danjulio/firecam/firecam_app/pictures/firecam_utility_wifi_mac.png

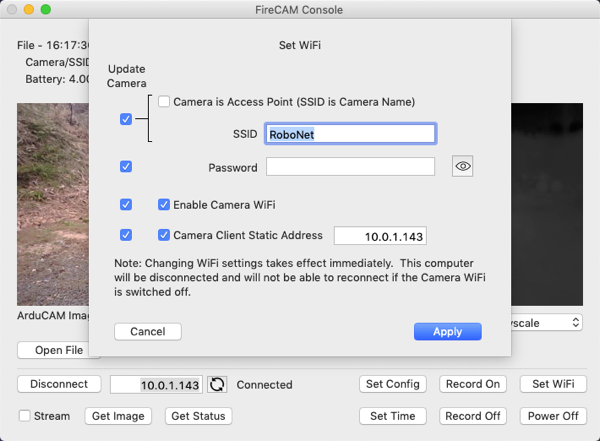
firecam_app/pictures/firecam_utility_wifi_mac.png
