danjulio/firecam/firmware/components/i2c/i2c.c

/*
 * I2C Module
 *
 * Provides I2C Access routines for other modules/tasks.  Provides a locking mechanism
 * since the underlying ESP IDF routines are not thread safe.
 *
 * Copyright 2020 Dan Julio
 *
 * This file is part of firecam.
 *
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
 */
#include "system_config.h"
#include "i2c.h"
#include "driver/i2c.h"
#include "freertos/FreeRTOS.h"
#include "freertos/semphr.h"


//
// I2C variables
//
static SemaphoreHandle_t i2c_mutex;



//
// I2C API
//

/**
 * i2c master initialization
 */
esp_err_t i2c_master_init()
{
    int i2c_master_port = I2C_MASTER_NUM;
    i2c_config_t conf;
    
    i2c_mutex = xSemaphoreCreateMutex();
    
    conf.mode = I2C_MODE_MASTER;
    conf.sda_io_num = I2C_MASTER_SDA_IO;
    conf.sda_pullup_en = GPIO_PULLUP_ENABLE;
    conf.scl_io_num = I2C_MASTER_SCL_IO;
    conf.scl_pullup_en = GPIO_PULLUP_ENABLE;
    conf.master.clk_speed = I2C_MASTER_FREQ_HZ;
    
    i2c_param_config(i2c_master_port, &conf);
    
    return i2c_driver_install(i2c_master_port, conf.mode,
                              I2C_MASTER_RX_BUF_LEN,
                              I2C_MASTER_TX_BUF_LEN, 0);
}


/**
 * i2c master lock
 */
void i2c_lock()
{
	xSemaphoreTake(i2c_mutex, portMAX_DELAY);
}


/**
 * i2c master unlock
 */
void i2c_unlock()
{
	xSemaphoreGive(i2c_mutex);
}


/**
 * Read esp-i2c-slave
 *
 * _______________________________________________________________________________________
 * | start | slave_addr + rd_bit +ack | read n-1 bytes + ack | read 1 byte + nack | stop |
 * --------|--------------------------|----------------------|--------------------|------|
 *
 */
esp_err_t i2c_master_read_slave(uint8_t addr7, uint8_t *data_rd, size_t size)
{
    if (size == 0) {
        return ESP_OK;
    }
    i2c_cmd_handle_t cmd = i2c_cmd_link_create();
    i2c_master_start(cmd);
    i2c_master_write_byte(cmd, (addr7 << 1) | I2C_MASTER_READ, ACK_CHECK_EN);
    if (size > 1) {
        i2c_master_read(cmd, data_rd, size - 1, ACK_VAL);
    }
    i2c_master_read_byte(cmd, data_rd + size - 1, NACK_VAL);
    i2c_master_stop(cmd);
    esp_err_t ret = i2c_master_cmd_begin(I2C_MODE_MASTER, cmd, 1000 / portTICK_RATE_MS);
    i2c_cmd_link_delete(cmd);
    return ret;
}


/**
 * Write esp-i2c-slave
 *
 * ___________________________________________________________________
 * | start | slave_addr + wr_bit + ack | write n bytes + ack  | stop |
 * --------|---------------------------|----------------------|------|
 *
 */
esp_err_t i2c_master_write_slave(uint8_t addr7, uint8_t *data_wr, size_t size)
{
    i2c_cmd_handle_t cmd = i2c_cmd_link_create();
    i2c_master_start(cmd);
    i2c_master_write_byte(cmd, (addr7 << 1) | I2C_MASTER_WRITE, ACK_CHECK_EN);
    i2c_master_write(cmd, data_wr, size, ACK_CHECK_EN);
    i2c_master_stop(cmd);
    esp_err_t ret = i2c_master_cmd_begin(I2C_MODE_MASTER, cmd, 1000 / portTICK_RATE_MS);
    i2c_cmd_link_delete(cmd);
    return ret;
}
