danjulio/firecam/firmware/components/lvgl_ili9341/ili9341.c

/**
 * @file ili9341.c
 *
 * Official lvgl esp32 port, ported to firecam by Dan Julio
 */

/*********************
 *      INCLUDES
 *********************/
#include "ili9341.h"
#include "disp_spi.h"
#include "driver/gpio.h"
#include "esp_log.h"
#include "freertos/FreeRTOS.h"
#include "freertos/task.h"
#include "sys_utilities.h"

/*********************
 *      DEFINES
 *********************/

/**********************
 *      TYPEDEFS
 **********************/

/*The LCD needs a bunch of command/argument values to be initialized. They are stored in this struct. */
typedef struct {
    uint8_t cmd;
    uint8_t data[16];
    uint8_t databytes; //No of data in data; bit 7 = delay after set; 0xFF = end of cmds.
} lcd_init_cmd_t;

/**********************
 *  STATIC PROTOTYPES
 **********************/
static void ili9341_send_cmd(uint8_t cmd);
static void ili9341_send_data(void * data, uint16_t length);
static void ili9341_send_color(void * data, uint16_t length);

/**********************
 *  STATIC VARIABLES
 **********************/
static const char* TAG = "ili9341";

/**********************
 *      MACROS
 **********************/

/**********************
 *   GLOBAL FUNCTIONS
 **********************/

void ili9341_init(void)
{
	lcd_init_cmd_t ili_init_cmds[]={
		{0xCF, {0x00, 0x83, 0X30}, 3},
		{0xED, {0x64, 0x03, 0X12, 0X81}, 4},
		{0xE8, {0x85, 0x01, 0x79}, 3},
		{0xCB, {0x39, 0x2C, 0x00, 0x34, 0x02}, 5},
		{0xF7, {0x20}, 1},
		{0xEA, {0x00, 0x00}, 2},
		{0xC0, {0x26}, 1},			/*Power control*/
		{0xC1, {0x11}, 1},			/*Power control */
		{0xC5, {0x35, 0x3E}, 2},	/*VCOM control*/
		{0xC7, {0xBE}, 1},			/*VCOM control*/
		{0x36, {0x28}, 1},			/*Memory Access Control*/
		{0x3A, {0x55}, 1},			/*Pixel Format Set*/
		{0xB1, {0x00, 0x1B}, 2},
		{0xF2, {0x08}, 1},
		{0x26, {0x01}, 1},
		{0xE0, {0x1F, 0x1A, 0x18, 0x0A, 0x0F, 0x06, 0x45, 0X87, 0x32, 0x0A, 0x07, 0x02, 0x07, 0x05, 0x00}, 15},
		{0XE1, {0x00, 0x25, 0x27, 0x05, 0x10, 0x09, 0x3A, 0x78, 0x4D, 0x05, 0x18, 0x0D, 0x38, 0x3A, 0x1F}, 15},
		{0x2A, {0x00, 0x00, 0x00, 0xEF}, 4},
		{0x2B, {0x00, 0x00, 0x01, 0x3f}, 4},
		{0x2C, {0}, 0},
		{0xB7, {0x07}, 1},
		{0xB6, {0x0A, 0x82, 0x27, 0x00}, 4},
		{0x11, {0}, 0x80},
		{0x29, {0}, 0x80},
		{0, {0}, 0xff},
	};

	ESP_LOGI(TAG, "ILI9341 initialization");

	//Send all the commands
	uint16_t cmd = 0;
	while (ili_init_cmds[cmd].databytes!=0xff) {
		ili9341_send_cmd(ili_init_cmds[cmd].cmd);
		ili9341_send_data(ili_init_cmds[cmd].data, ili_init_cmds[cmd].databytes&0x1F);
		if (ili_init_cmds[cmd].databytes & 0x80) {
			vTaskDelay(pdMS_TO_TICKS(100));
		}
		cmd++;
	}

#if ILI9341_INVERT_DISPLAY
	uint8_t data[] = {0x68};
	// this same command also sets rotation (portrait/landscape) and inverts colors.
	// https://gist.github.com/motters/38a26a66020f674b6389063932048e4c#file-ili9844_defines-h-L24
	ili9341_send_cmd(0x36);
	ili9341_send_data(&data, 1);
#endif
}


void ili9341_flush(lv_disp_drv_t * drv, const lv_area_t * area, lv_color_t * color_map)
{
	uint8_t data[4];
	
	system_lock_vspi();

	/*Column addresses*/
	ili9341_send_cmd(0x2A);
	data[0] = (area->x1 >> 8) & 0xFF;
	data[1] = area->x1 & 0xFF;
	data[2] = (area->x2 >> 8) & 0xFF;
	data[3] = area->x2 & 0xFF;
	ili9341_send_data(data, 4);

	/*Page addresses*/
	ili9341_send_cmd(0x2B);
	data[0] = (area->y1 >> 8) & 0xFF;
	data[1] = area->y1 & 0xFF;
	data[2] = (area->y2 >> 8) & 0xFF;
	data[3] = area->y2 & 0xFF;
	ili9341_send_data(data, 4);

	/*Memory write*/
	ili9341_send_cmd(0x2C);


	uint32_t size = lv_area_get_width(area) * lv_area_get_height(area);

	ili9341_send_color((void*)color_map, size * 2);
	
	system_unlock_vspi();
}



/**********************
 *   STATIC FUNCTIONS
 **********************/


static void ili9341_send_cmd(uint8_t cmd)
{
	while (disp_spi_is_busy()) {
		taskYIELD();
	};

	gpio_set_level(ILI9341_DC, 0);	 /*Command mode*/
	disp_spi_send_data(&cmd, 1);
}

static void ili9341_send_data(void * data, uint16_t length)
{
	while (disp_spi_is_busy()) {
		taskYIELD();
	};

	gpio_set_level(ILI9341_DC, 1);	 /*Data mode*/
	disp_spi_send_data(data, length);
}

static void ili9341_send_color(void * data, uint16_t length)
{
	while (disp_spi_is_busy()) {
		taskYIELD();
	};

    gpio_set_level(ILI9341_DC, 1);   /*Data mode*/
    disp_spi_send_colors(data, length);
}
