danjulio/firecam/firmware/components/sys/sys_utilities.c

/*
 * System related utilities
 *
 * Contains functions to initialize the system, other utility functions and a set
 * of globally available handles for the various tasks (to use for task notifications).
 *
 * Copyright 2020 Dan Julio
 *
 * This file is part of firecam.
 *
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
 */
#include "esp_system.h"
#include "esp_log.h"
#include "esp_heap_caps.h"
#include "freertos/FreeRTOS.h"
#include "freertos/semphr.h"
#include "driver/spi_master.h"
#include "system_config.h"
#include "adc_utilities.h"
#include "file_utilities.h"
#include "json_utilities.h"
#include "lepton_utilities.h"
#include "ps_utilities.h"
#include "sys_utilities.h"
#include "time_utilities.h"
#include "wifi_utilities.h"
#include "gui_screen_main.h"
#include "i2c.h"
#include "palettes.h"
#include "ov2640.h"
#include "render_jpg.h"
#include "vospi.h"



//
// System Utilities variables
//
static const char* TAG = "sys";


// Recording intervals
const record_interval_t record_intervals[REC_INT_NUM] = {
	{
		.name = REC_INT_0_NAME,
		.interval = REC_INT_0_VAL
	},
	{
		.name = REC_INT_1_NAME,
		.interval = REC_INT_1_VAL
	},
	{
		.name = REC_INT_2_NAME,
		.interval = REC_INT_2_VAL
	},
	{
		.name = REC_INT_3_NAME,
		.interval = REC_INT_3_VAL
	},
	{
		.name = REC_INT_4_NAME,
		.interval = REC_INT_4_VAL
	},
	{
		.name = REC_INT_5_NAME,
		.interval = REC_INT_5_VAL
	},
	{
		.name = REC_INT_6_NAME,
		.interval = REC_INT_6_VAL
	}
};



//
// Task handle externs for use by tasks to communicate with each other
//
TaskHandle_t task_handle_adc;
TaskHandle_t task_handle_app;
TaskHandle_t task_handle_cam;
TaskHandle_t task_handle_cmd;
TaskHandle_t task_handle_file;
TaskHandle_t task_handle_gui;
TaskHandle_t task_handle_lep;
#ifdef INCLUDE_SYS_MON
TaskHandle_t task_handle_mon;
#endif


//
// Global buffer pointers for memory allocated in the external SPIRAM
//

// Shared memory data structures
cam_buffer_t sys_cam_buffer;   // Loaded by cam_task with jpeg data for other tasks
lep_buffer_t sys_lep_buffer;   // Loaded by lep_task for other task
json_image_string_t sys_image_file_buffer;   // Loaded by app_task with image data for file_task
json_image_string_t sys_cmd_response_buffer; // Loaded by app_task with image data for cmd_task
gui_state_t gui_st;            // Shared GUI control variables

// Big buffers
uint16_t* gui_cam_bufferP;    // Loaded by gui_task for its own use
uint16_t* gui_lep_bufferP;    // Loaded by gui_task for its own use

// Designed to lock VSPI for multiple uninterruptible SPI transactions by one task
static SemaphoreHandle_t vspi_mutex;



//
// System Utilities API
//

/**
 * Initialize the ESP32 GPIO and internal peripherals
 */
bool system_esp_io_init()
{
	ESP_LOGI(TAG, "ESP32 Peripheral Initialization");
	
	// First thing to do is set PWR_HOLD to keep system powered after power button released
	gpio_set_direction(PWR_HOLD_IO, GPIO_MODE_OUTPUT);
	gpio_set_level(PWR_HOLD_IO, 1);
	
	// Configure other GPIO pins
	gpio_set_direction(CAM_CSN_IO, GPIO_MODE_OUTPUT);
	gpio_set_level(CAM_CSN_IO, 1);
	gpio_set_direction(LCD_CSN_IO, GPIO_MODE_OUTPUT);
	gpio_set_level(LCD_CSN_IO, 1);
	gpio_set_direction(LEP_CSN_IO, GPIO_MODE_OUTPUT);
	gpio_set_level(LEP_CSN_IO, 1);
	gpio_set_direction(TS_CSN_IO, GPIO_MODE_OUTPUT);
	gpio_set_level(TS_CSN_IO, 1);
	gpio_set_direction(LCD_DC_IO, GPIO_MODE_OUTPUT);
	gpio_set_level(LCD_DC_IO, 0);
	gpio_set_direction(TS_IRQ_IO, GPIO_MODE_INPUT);
	gpio_set_direction(LEP_VSYNC_IO, GPIO_MODE_INPUT);
	
	// Handle the special case where the DS3232 RTC I2C interface is confused.
	// Per its data sheet, we manually toggle SCL until SDA is seen high.
	// Do this before handing the pins over the I2C interface during its initialization.
	
	
	// Attempt to initialize the I2C Master
	if (i2c_master_init() != ESP_OK) {
		ESP_LOGE(TAG, "I2C Master initialization failed");
		return false;
	}
	
	// Attempt to initialize the HSPI Master (used by the Lepton)
	spi_bus_config_t hspi_buscfg = {
		.miso_io_num=HSPI_MISO_IO,
		.mosi_io_num=-1,
		.sclk_io_num=HSPI_SCK_IO,
		.max_transfer_sz=LEP_PKT_LENGTH,
		.quadwp_io_num=-1,
		.quadhd_io_num=-1
	};
	if (spi_bus_initialize(HSPI_HOST, &hspi_buscfg, HSPI_DMA_NUM) != ESP_OK) {
		ESP_LOGE(TAG, "HSPI Master initialization failed");
		return false;
	}
	
	// Attempt to initialize the VSPI Master (used by the ArduCAM, LCD and Touchscreen)
	// Maximum transfer size is set by the LVGL display buffer (that is larger than
	// packets transferred for the ArduCAM or Touchscreen).
	spi_bus_config_t vspi_buscfg = {
		.miso_io_num=VSPI_MISO_IO,
		.mosi_io_num=VSPI_MOSI_IO,
		.sclk_io_num=VSPI_SCK_IO,
		.max_transfer_sz=LVGL_DISP_BUF_SIZE * 2,
		.quadwp_io_num=-1,
		.quadhd_io_num=-1
	};
	if (spi_bus_initialize(VSPI_HOST, &vspi_buscfg, VSPI_DMA_NUM) != ESP_OK) {
		ESP_LOGE(TAG, "VSPI Master initialization failed");
		return false;
	}
	
	return true;
}


/**
 * Initialize the board-level peripheral subsystems
 */
bool system_peripheral_init()
{
	ESP_LOGI(TAG, "System Peripheral Initialization");
	
	// Time and PS init first so other modules can use data from them
	time_init();
	ps_init();
	
	if (!adc_init()) {
		ESP_LOGE(TAG, "ADC subsystem initialization failed");
		return false;
	}
	
	if (ov2640_init() == 0) {
		ESP_LOGE(TAG, "Arducam ov2640 initialization failed");
		return false;
	}

	if (!lepton_init()) {
		ESP_LOGE(TAG, "Lepton initialization failed");
		return false;
	}
	if (vospi_init() != ESP_OK) {
		ESP_LOGE(TAG, "Lepton VoSPI initialization failed");
		return false;
	}
	
	if (!file_init_sdmmc_driver()) {
		ESP_LOGE(TAG, "SD Card driver initialization failed");
		return false;
	}
	
	if (!wifi_init()) {
		ESP_LOGE(TAG, "WiFi initialization failed");
		return false;
	}
	
	return true;
}


/**
 * Allocate shared buffers for use by tasks for image data
 */
bool system_buffer_init()
{
	uint16_t* ptr;
	
	ESP_LOGI(TAG, "Buffer Allocation");
	
	// Allocate the ArduCAM jpeg image buffer in the external RAM
	sys_cam_buffer.cam_bufferP = heap_caps_malloc(CAM_MAX_JPG_LEN, MALLOC_CAP_SPIRAM);
	if (sys_cam_buffer.cam_bufferP == NULL) {
		ESP_LOGE(TAG, "malloc ArduCAM shared buffer failed");
		return false;
	}
	
	// Allocate the buffer used by the gui to display images from the ArduCAM
	gui_cam_bufferP = heap_caps_malloc(CAM_IMG_PIXELS*2, MALLOC_CAP_SPIRAM);
	if (gui_cam_bufferP == NULL) {
		ESP_LOGE(TAG, "malloc ArduCAM gui buffer failed");
		return false;
	}
	
	// Clear ArduCAM display buffer (to color black)
	ptr = gui_cam_bufferP;
	while (ptr < (gui_cam_bufferP + CAM_IMG_PIXELS)) {
		*ptr++ = 0;
	}
	
	// Allocate the lepton frame buffer in the external RAM
	sys_lep_buffer.lep_bufferP = heap_caps_malloc(LEP_NUM_PIXELS*2, MALLOC_CAP_SPIRAM);
	if (sys_lep_buffer.lep_bufferP == NULL) {
		ESP_LOGE(TAG, "malloc lepton shared image buffer failed");
		return false;
	}
		
	// Allocate the lepton telemetry buffer in the external RAM
	sys_lep_buffer.lep_telemP = heap_caps_malloc(LEP_TEL_WORDS*2, MALLOC_CAP_SPIRAM);
	if (sys_lep_buffer.lep_telemP == NULL) {
		ESP_LOGE(TAG, "malloc lepton shared telemetry buffer failed");
		return false;
	}
	
	// Allocate the buffer used by the gui to display images from the lepton
	gui_lep_bufferP = heap_caps_malloc(LEP_IMG_PIXELS*2, MALLOC_CAP_SPIRAM);
	if (gui_lep_bufferP == NULL) {
		ESP_LOGE(TAG, "malloc lepton gui buffer failed");
		return false;
	}
	// Clear lepton display buffer (to color black)
	ptr = gui_lep_bufferP;
	while (ptr < (gui_lep_bufferP + LEP_IMG_PIXELS)) {
		*ptr++ = 0;
	}
	
	// Allocate the work area for the jpeg decompressor
	if (!render_init()) {
		ESP_LOGE(TAG, "initialize jpeg decompressor failed");
		return false;
	}
	
	// Allocate the json buffers
	if (!json_init()) {
		ESP_LOGE(TAG, "malloc json buffers failed");
		return false;
	}
	
	// Allocate the shared json image text buffers in the external RAM
	sys_image_file_buffer.bufferP = heap_caps_malloc(JSON_MAX_IMAGE_TEXT_LEN, MALLOC_CAP_SPIRAM);
	if (sys_image_file_buffer.bufferP == NULL) {
		ESP_LOGE(TAG, "malloc shared json image text file buffer failed");
		return false;
	}
	sys_cmd_response_buffer.bufferP = heap_caps_malloc(JSON_MAX_IMAGE_TEXT_LEN, MALLOC_CAP_SPIRAM);
	if (sys_cmd_response_buffer.bufferP == NULL) {
		ESP_LOGE(TAG, "malloc shared json image text command buffer failed");
		return false;
	}
	
	// Create the VSPI SPI Bus mutex
	vspi_mutex = xSemaphoreCreateMutex();
	if (vspi_mutex == NULL) {
		ESP_LOGE(TAG, "could not create vspi_mutex");
		return false;
	}
	
	// Initialize GUI state (that may be used by other modules) from persistent storage
	ps_get_gui_state(&gui_st);
	
	return true;
}


/**
 * Shut the system off
 */
void system_shutoff()
{
	ESP_LOGI(TAG, "shutdown");
	
	// Delay for final logging
	vTaskDelay(pdMS_TO_TICKS(10));
	
	// Commit Seppuku
	gpio_set_level(PWR_HOLD_IO, 0);
}


/**
 * Lock the VSPI SPI bus
 */
void system_lock_vspi()
{
	xSemaphoreTake(vspi_mutex, portMAX_DELAY);
}


/**
 * Unlock the VSPI SPI bus
 */
void system_unlock_vspi()
{
	xSemaphoreGive(vspi_mutex);
}


/**
 * Attempt to find the specified recording interval in record_intervals, otherwise return -1
 */
int system_get_rec_interval_index(int rec_interval)
{
	int i;
	
	for (i=0; i<REC_INT_NUM; i++) {
		if (rec_interval == record_intervals[i].interval) {
			return i;
		}
	}
	
	return -1;
}
