danjulio/firecam/firmware/components/clock/time_utilities.c

/*
 * Time related utilities
 *
 * Contains functions to interface the RTC to the system timekeeping
 * capabilities and provide application access to the system time.
 *
 * Copyright 2020 Dan Julio
 *
 * This file is part of firecam.
 *
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
 */
#include "time_utilities.h"
#include "esp_system.h"
#include "esp_log.h"
#include <stdlib.h>
#include <time.h>
#include <sys/time.h>


//
// Time Utilities date related strings (related to tmElements)
//
static const char* day_strings[] = {
	"Err",
	"Sun",
	"Mon",
	"Tue",
	"Wed",
	"Thu",
	"Fri",
	"Sat"
};

static const char* mon_strings[] = {
	"Err",
	"Jan",
	"Feb",
	"Mar",
	"Apr",
	"May",
	"Jun",
	"Jul",
	"Aug",
	"Sep",
	"Oct",
	"Nov",
	"Dec"
};


//
// Time Utilities Variables
//
static const char* TAG = "time_utilities";


 
//
// Time Utilities API
//

/**
 * Initialize system time from the RTC
 */
void time_init()
{
	char buf[26];
	tmElements_t te;
	struct timeval tv;
	time_t secs;
	
	// Set the system time from the RTC
	secs = get_rtc_time_secs();
	tv.tv_sec = secs;
	tv.tv_usec = 0;
	settimeofday((const struct timeval *) &tv, NULL);
	
	// Diagnostic display of time
	time_get(&te);
	time_get_disp_string(te, buf);
	ESP_LOGI(TAG, "Initial RTC time: %s", buf);
}


/**
 * Set the system time and update the RTC
 */
void time_set(tmElements_t te)
{
	struct timeval tv;
	time_t secs;
	
	// Attempt to set the RTC
	if (write_rtc_time(te) != 0) {
		ESP_LOGE(TAG, "Update RTC failed");
	}
	
	// Set the system time
	secs = rtc_makeTime(te);
	tv.tv_sec = secs;
	tv.tv_usec = 0;
	settimeofday((const struct timeval *) &tv, NULL);
}


/**
 * Get the system time
 */
void time_get(tmElements_t* te)
{
	time_t now;
	struct tm timeinfo;
	
	// Get the time and convert into our simplified tmElements format
	time(&now);
    localtime_r(&now, &timeinfo);  // Get the unix formatted timeinfo
    mktime(&timeinfo);             // Fill in the DOW and DOY fields
    te->Second = (uint8_t) timeinfo.tm_sec;
    te->Minute = (uint8_t) timeinfo.tm_min;
    te->Hour = (uint8_t) timeinfo.tm_hour;
    te->Wday = (uint8_t) timeinfo.tm_wday + 1; // Sunday is 1 in our tmElements structure
    te->Day = (uint8_t) timeinfo.tm_mday;
    te->Month = (uint8_t) timeinfo.tm_mon + 1; // January is 1 in our tmElements structure
    te->Year = (uint8_t) timeinfo.tm_year - 70; // tmElements starts at 1970
}


/**
 * Return true if the system time (in seconds) has changed from the last time
 * this function returned true. Each calling task must maintain its own prev_time
 * variable (it can initialize it to 0).  Set te to NULL if you don't need the time.
 */
bool time_changed(tmElements_t* te, time_t* prev_time)
{
	time_t now;
	struct tm timeinfo;
	
	// Get the time and check if it is different
	time(&now);
	if (now != *prev_time) {
		*prev_time = now;
		
		if (te != NULL) {
			// convert time into our simplified tmElements format
    		localtime_r(&now, &timeinfo);  // Get the unix formatted timeinfo
    		mktime(&timeinfo);             // Fill in the DOW and DOY fields
    		te->Second = (uint8_t) timeinfo.tm_sec;
    		te->Minute = (uint8_t) timeinfo.tm_min;
    		te->Hour = (uint8_t) timeinfo.tm_hour;
    		te->Wday = (uint8_t) timeinfo.tm_wday + 1; // Sunday is 1 in our tmElements structure
    		te->Day = (uint8_t) timeinfo.tm_mday;
    		te->Month = (uint8_t) timeinfo.tm_mon + 1; // January is 1 in our tmElements structure
    		te->Year = (uint8_t) timeinfo.tm_year - 70; // tmElements starts at 1970
    	}
    	
    	return true;
    } else {
    	return false;
    }
}


/**
 * Load buf with a time & date string for display.
 *
 *   "DOW MON DAY HH:MM:SS YEAR"
 *
 * buf must be at least 26 bytes long (to include null termination).
 */
void time_get_disp_string(tmElements_t te, char* buf)
{
	// Validate te to prevent illegal accesses to the constant string buffers
	if (te.Wday > 7) te.Wday = 0;
	if (te.Month > 12) te.Month = 0;
	
	// Build up the string
	sprintf(buf,"%s %s %2d %2d:%02d:%02d %4d", 
		day_strings[te.Wday],
		mon_strings[te.Month],
		te.Day,
		te.Hour,
		te.Minute,
		te.Second,
		te.Year + 1970);
}


/**
 * Load buf with a short time & date string with no spaces.  Useful for constructing
 * a file or directory name.
 *
 *   "YY_MM_DD_HH_MM_SS"
 *
 * buf must be at least 18 characters long (to include null termination)
 */
void time_get_short_string(tmElements_t te, char* buf)
{
	// Always assume we are running post 2000
	te.Year = tmYearToY2k(te.Year);
	
	// Build up the string
	sprintf(buf, "%2d_%02d_%02d_%02d_%02d_%02d",
		te.Year, te.Month, te.Day, te.Hour, te.Minute, te.Second);
}
